busycircuits/alm012-sid-guts-deluxe/firmware/lookup.h

const unsigned int volts_to_fnum[] PROGMEM = {
290, 291, 291, 292, 292, 293, 293, 294, 294, 
295, 295, 296, 296, 297, 297, 298, 298, 
299, 299, 300, 300, 301, 301, 302, 302, 
303, 303, 304, 304, 305, 305, 306, 306, 
307, 307, 308, 308, 309, 309, 310, 310, 
311, 311, 312, 313, 313, 314, 314, 315, 
315, 316, 316, 317, 317, 318, 318, 319, 
320, 320, 321, 321, 322, 322, 323, 323, 
324, 324, 325, 326, 326, 327, 327, 328, 
328, 329, 329, 330, 331, 331, 332, 332, 
333, 333, 334, 334, 335, 336, 336, 337, 
337, 338, 338, 339, 340, 340, 341, 341, 
342, 342, 343, 344, 344, 345, 345, 346, 
347, 347, 348, 348, 349, 350, 350, 351, 
351, 352, 353, 353, 354, 354, 355, 356, 
356, 357, 357, 358, 359, 359, 360, 360, 
361, 362, 362, 363, 363, 364, 365, 365, 
366, 367, 367, 368, 368, 369, 370, 370, 
371, 372, 372, 373, 373, 374, 375, 375, 
376, 377, 377, 378, 379, 379, 380, 380, 
381, 382, 382, 383, 384, 384, 385, 386, 
386, 387, 388, 388, 389, 390, 390, 391, 
392, 392, 393, 394, 394, 395, 396, 396, 
397, 398, 398, 399, 400, 400, 401, 402, 
402, 403, 404, 404, 405, 406, 406, 407, 
408, 408, 409, 410, 411, 411, 412, 413, 
413, 414, 415, 415, 416, 417, 418, 418, 
419, 420, 420, 421, 422, 423, 423, 424, 
425, 425, 426, 427, 428, 428, 429, 430, 
431, 431, 432, 433, 433, 434, 435, 436, 
436, 437, 438, 439, 439, 440, 441, 442, 
442, 443, 444, 445, 445, 446, 447, 448, 
448, 449, 450, 451, 451, 452, 453, 454, 
455, 455, 456, 457, 458, 458, 459, 460, 
461, 461, 462, 463, 464, 465, 465, 466, 
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
26, 26, 26, 26, 26, 26, 27, 27, 
27, 27, 27, 27, 27, 27, 27, 27, 
27, 27, 27, 27, 27, 27, 27, 27, 
27, 27, 27, 28, 28, 28, 28, 28, 
28, 28, 28, 28, 28, 28, 28, 28, 
28, 28, 28, 28, 28, 28, 28, 28, 
29, 29, 29, 29, 29, 29, 29, 29, 
29, 29, 29, 29, 29, 29, 29, 29, 
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
